cshariq/Serene/BOM/BOM Checkout Pictures/Picture2.png

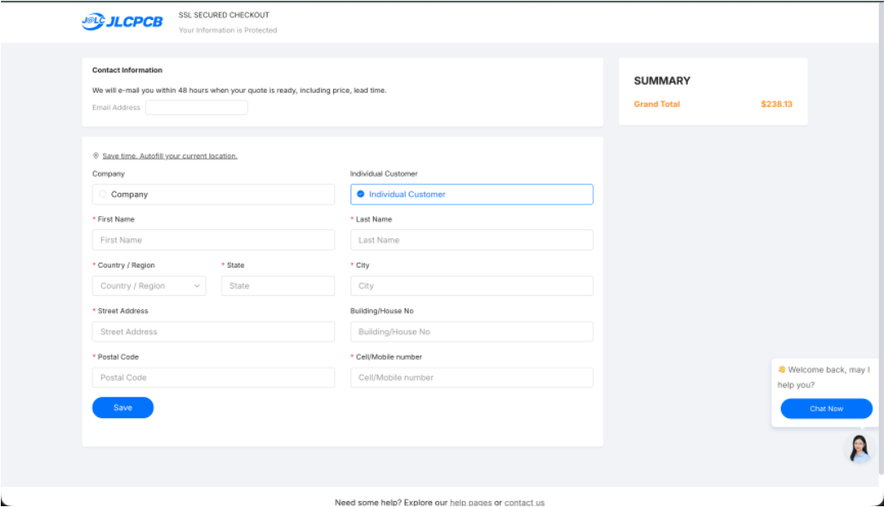
BOM/BOM Checkout Pictures/Picture2.png
