cshariq/Serene/BOM/BOM Checkout Pictures/Picture3.png

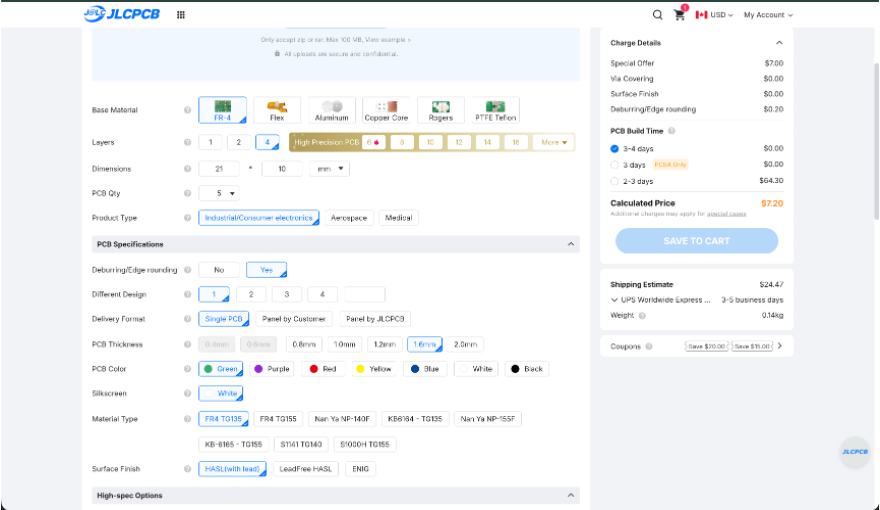
BOM/BOM Checkout Pictures/Picture3.png
