cshariq/Serene/BOM/BOM Checkout Pictures/Picture6.png

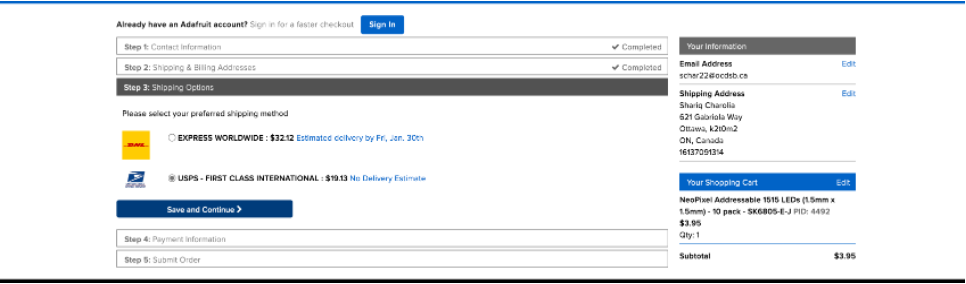
BOM/BOM Checkout Pictures/Picture6.png
