cshariq/Serene/BOM/BOM Checkout Pictures/Picture7.png

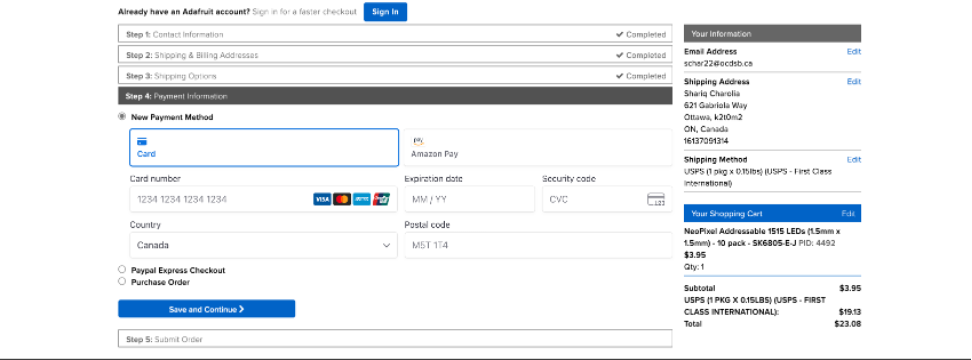
BOM/BOM Checkout Pictures/Picture7.png
