cshariq/Serene/BOM/BOM Checkout Pictures/Picture8.png

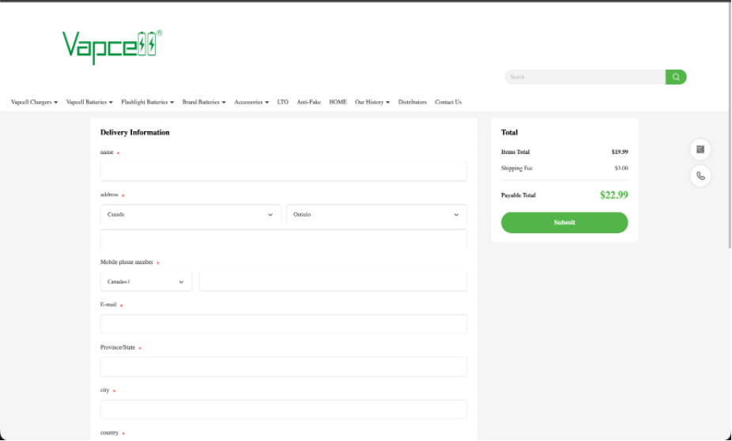
BOM/BOM Checkout Pictures/Picture8.png
